brianodermatt/wake-up-light/schematics/power-setup/power-setup.kicad_sch

## KiCad design schematics/power-setup/power-setup.kicad_sch (2022-02-27)

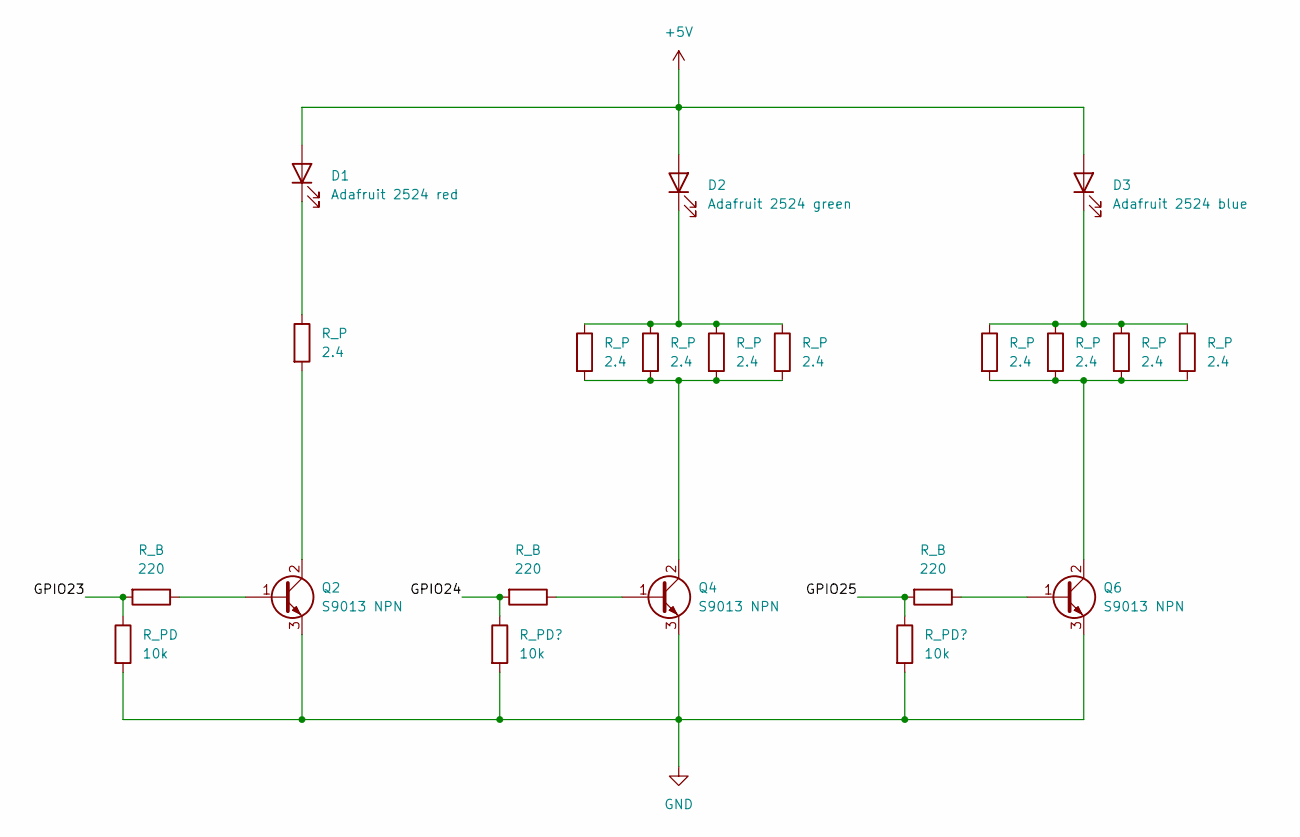
[picture p6: schematic power-setup.kicad_sch]

Parts:
D1: Adafruit 2524 red
D2: Adafruit 2524 green
D3: Adafruit 2524 blue
Q2, Q4, Q6: S9013 NPN
R_B: 220
R_P: 2.4
R_PD: 10k

Connections:
GPIO23: R_B.2, R_PD.1
GPIO24: R_B.2
GPIO25: R_B.2
unnamed: D1.1 (K), R_P.1
unnamed: D1.2 (A), D2.2 (A), D3.2 (A)
unnamed: D2.1 (K), R_P.1
unnamed: D3.1 (K), R_P.1
unnamed: Q2.1 (B), R_B.1
unnamed: Q2.2 (C), R_P.2
unnamed: Q2.3 (E), Q4.3 (E), Q6.3 (E), R_PD.2
unnamed: Q4.1 (B), R_B.1
unnamed: Q4.2 (C), R_P.2
unnamed: Q6.1 (B), R_B.1
unnamed: Q6.2 (C), R_P.2
