brianodermatt/wake-up-light/schematics/test-setup/test-setup.kicad_sch

## KiCad design schematics/test-setup/test-setup.kicad_sch (2022-01-28)

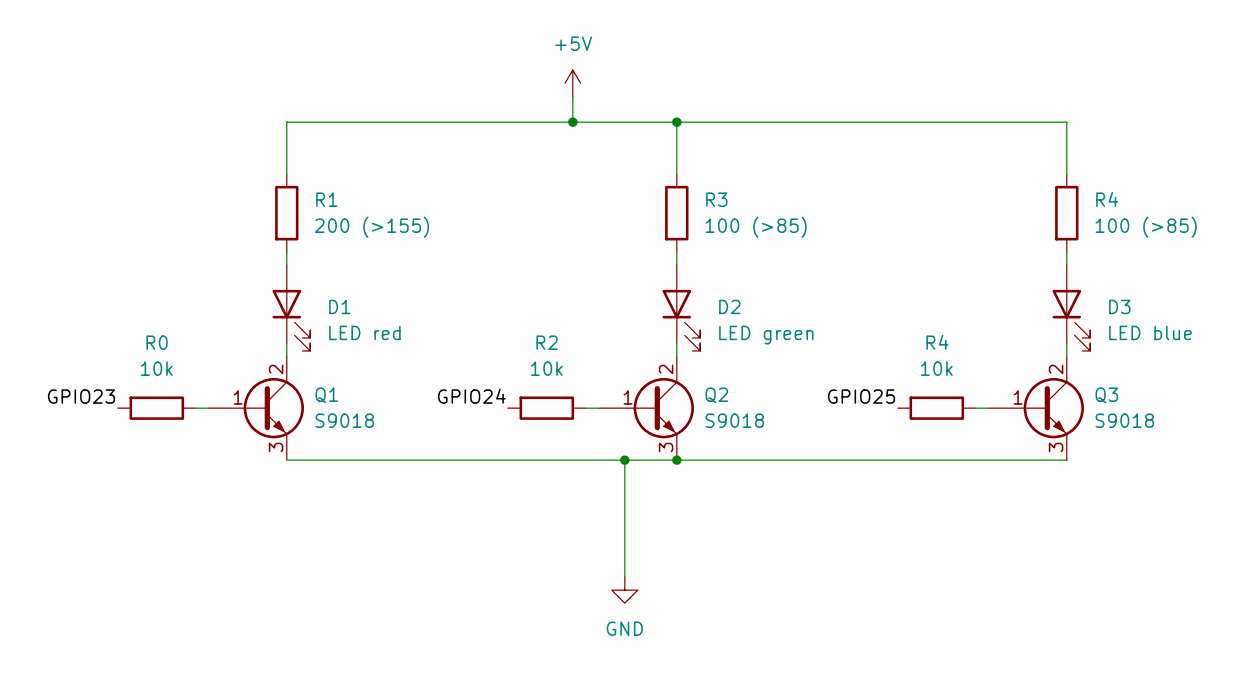
[picture p7: schematic test-setup.kicad_sch]

Parts:
D1: LED red
D2: LED green
D3: LED blue
Q1, Q2, Q3: S9018
R0, R2, R4: 10k
R1: 200 (>155)
R3: 100 (>85)

Connections:
GPIO23: R0.2
GPIO24: R2.2
GPIO25: R4.2
unnamed: D1.1 (K), Q1.2 (C)
unnamed: D1.2 (A), R1.2
unnamed: D2.1 (K), Q2.2 (C)
unnamed: D2.2 (A), R3.2
unnamed: D3.1 (K), Q3.2 (C)
unnamed: D3.2 (A), R4.2
unnamed: Q1.1 (B), R0.1
unnamed: Q1.3 (E), Q2.3 (E), Q3.3 (E)
unnamed: Q2.1 (B), R2.1
unnamed: Q3.1 (B), R4.1
unnamed: R1.1, R3.1, R4.1
